v9938/ESE_PAC/PCB/Image2.jpg

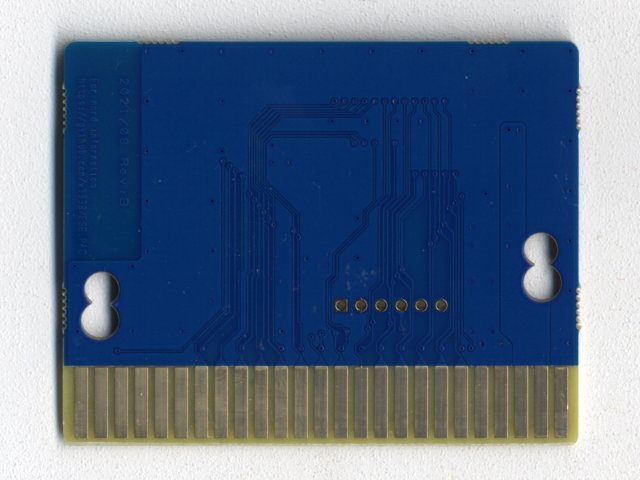
PCB/Image2.jpg
